open-lv/air-guard/docs/ka-lodet-karte.jpg

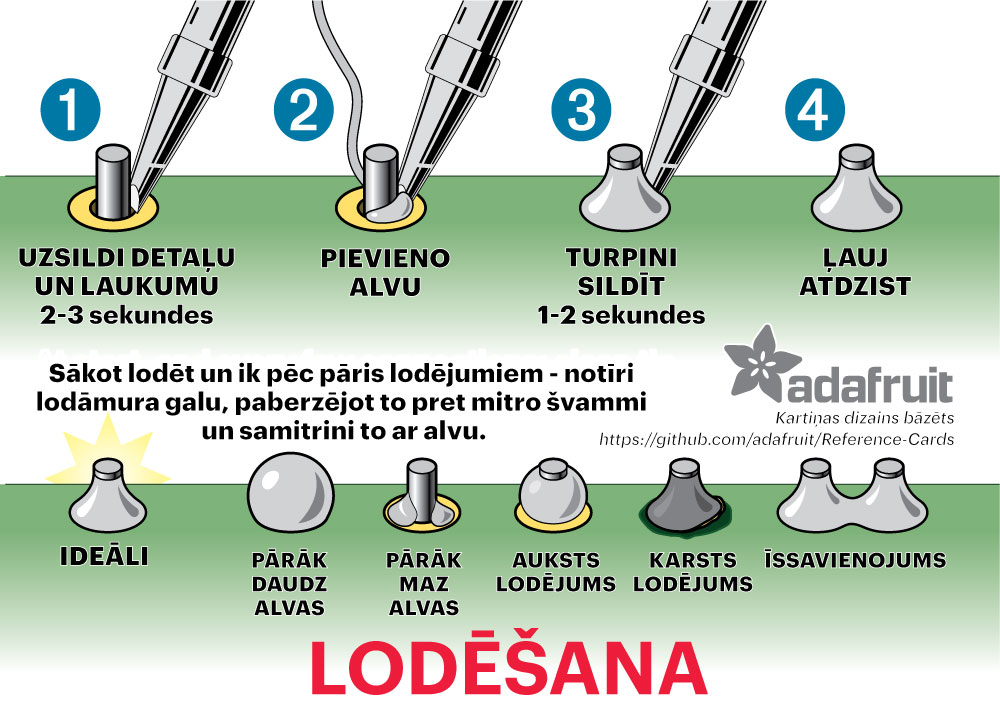
docs/ka-lodet-karte.jpg
